TudorSupica/DST-2/KiCAD files/DST-2.kicad_sch

## KiCad design KiCAD files/DST-2.kicad_sch (2025-04-01)

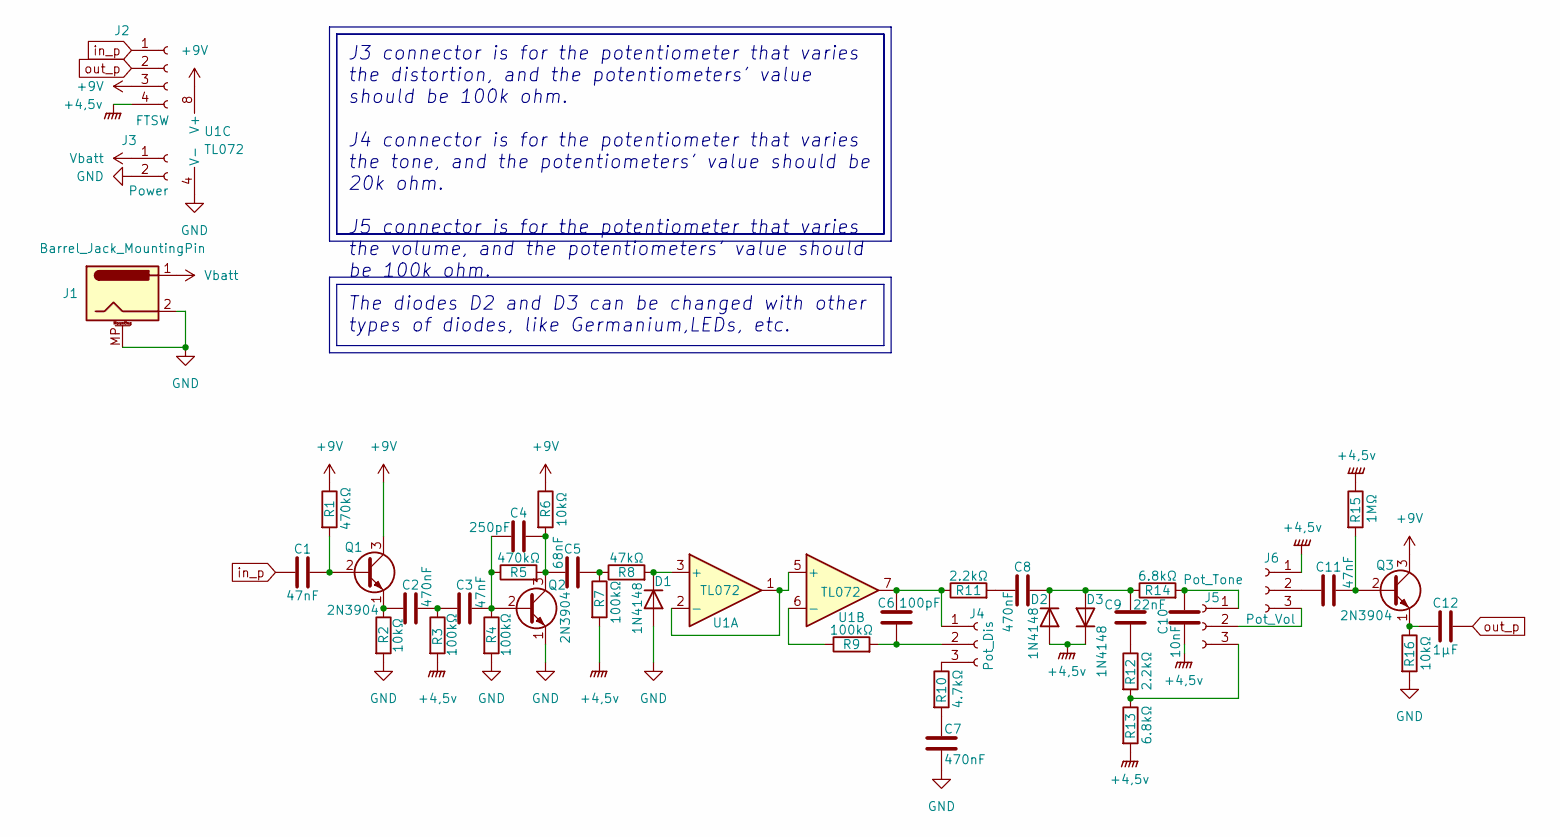
[picture p8: schematic DST-2.kicad_sch]

Parts:
C1, C3, C11: 47nF; C_0603_1608Metric_Pad1.08x0.95mm_HandSolder
C2, C7, C8: 470nF; C_0603_1608Metric_Pad1.08x0.95mm_HandSolder
C4: 250pF; C_0603_1608Metric_Pad1.08x0.95mm_HandSolder
C5: 68nF; C_0603_1608Metric_Pad1.08x0.95mm_HandSolder
C6: 100pF; C_0603_1608Metric_Pad1.08x0.95mm_HandSolder
C9: 22nF; C_0603_1608Metric_Pad1.08x0.95mm_HandSolder
C10: 10nF; C_0603_1608Metric_Pad1.08x0.95mm_HandSolder
C12: 1µF; C_0603_1608Metric_Pad1.08x0.95mm_HandSolder
D1, D2, D3: 1N4148; D_DO-35_SOD27_P7.62mm_Horizontal
J1: Barrel_Jack_MountingPin; BarrelJack_Kycon_KLDX-0202-xC_Horizontal
J2: FTSW; JST_XH_B4B-XH-A_1x04_P2.50mm_Vertical
J3: Power; JST_XH_B2B-XH-A_1x02_P2.50mm_Vertical
J4: Pot_Dis; JST_XH_B3B-XH-A_1x03_P2.50mm_Vertical
J5: Pot_Tone; JST_XH_B3B-XH-A_1x03_P2.50mm_Vertical
J6: Pot_Vol; JST_XH_B3B-XH-A_1x03_P2.50mm_Vertical
Q1, Q2, Q3: 2N3904; TO-92_Inline
R1, R5: 470kΩ; R_0603_1608Metric_Pad0.98x0.95mm_HandSolder
R2, R6, R16: 10kΩ; R_0603_1608Metric_Pad0.98x0.95mm_HandSolder
R3, R4, R7, R9: 100kΩ; R_0603_1608Metric_Pad0.98x0.95mm_HandSolder
R8: 47kΩ; R_0603_1608Metric_Pad0.98x0.95mm_HandSolder
R10: 4.7kΩ; R_0603_1608Metric_Pad0.98x0.95mm_HandSolder
R11, R12: 2.2kΩ; R_0603_1608Metric_Pad0.98x0.95mm_HandSolder
R13, R14: 6.8kΩ; R_0603_1608Metric_Pad0.98x0.95mm_HandSolder
R15: 1MΩ; R_0603_1608Metric_Pad0.98x0.95mm_HandSolder
U1: TL072; DIP-8_W8.89mm_SMDSocket_LongPads

Connections:
+4,5v: C10.1, D2.2 (A), D3.1 (K), J2.4, J6.1, R3.2, R7.2, R13.2, R15.1
+9V: J2.3, Q1.3 (C), Q3.3 (C), R1.1, R6.1, U1.8 (V+)
GND: C7.2, D1.2 (A), J1.2, J1.MP (MountPin), J3.2, Q2.1 (E), R2.2, R4.2, R16.2, U1.4 (V-)
unnamed: C1.2, Q1.2 (B), R1.2
unnamed: C2.1, Q1.1 (E), R2.1
unnamed: C2.2, C3.1, R3.1
unnamed: C3.2, C4.1, Q2.2 (B), R4.1, R5.1
unnamed: C4.2, C5.1, Q2.3 (C), R5.2, R6.2
unnamed: C5.2, R7.1, R8.1
unnamed: C6.1, J4.1, R11.1, U1.7
unnamed: C6.2, J4.2, R9.2
unnamed: C7.1, R10.2
unnamed: C8.1, R11.2
unnamed: C8.2, C9.1, D2.1 (K), D3.2 (A), R14.1
unnamed: C9.2, R12.1
unnamed: C10.2, J5.1, R14.2
unnamed: C11.1, J6.2
unnamed: C11.2, Q3.2 (B), R15.2
unnamed: C12.1, Q3.1 (E), R16.1
unnamed: D1.1 (K), R8.2, U1.3 (+)
unnamed: J4.3, R10.1
unnamed: J5.2, J6.3
unnamed: J5.3, R12.2, R13.1
unnamed: R9.1, U1.6 (-)
unnamed: U1.1, U1.2 (-), U1.5 (+)
Vbatt: J1.1, J3.1
in_p: C1.1, J2.1
out_p: C12.2, J2.2

Notes on the sheet:
J3 connector is for the potentiometer that varies the distortion, and the potentiometers' value should be 100k ohm. J4 connector is for the potentiometer that varies the tone, and the potentiometers' value should be 20k ohm. J5 connector is for the potentiometer that varies the volume, and the pote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
The diodes D2 and D3 can be changed with other types of diodes, like Germanium,LEDs, etc.
